TikoTikTok/bsidestlv-2026-badge/assets/characters/alice/alice_walk_sheet.png

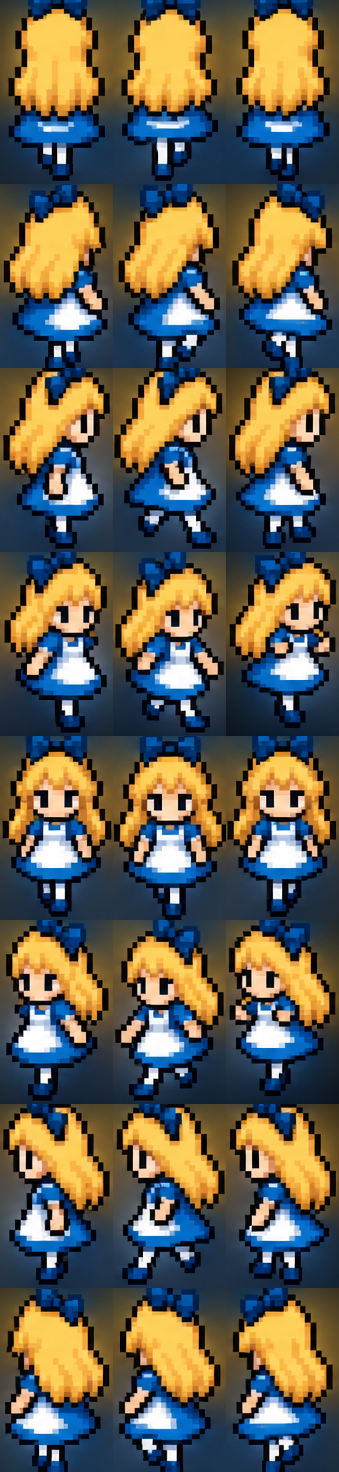
assets/characters/alice/alice_walk_sheet.png
