TikoTikTok/bsidestlv-2026-badge/software/dist/atlas.png

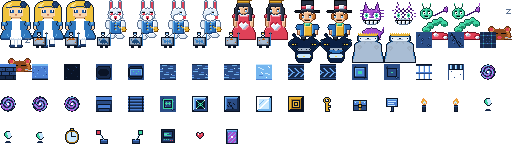
software/dist/atlas.png
