TikoTikTok/bsidestlv-2026-badge/software/dist/contact-sheet.png

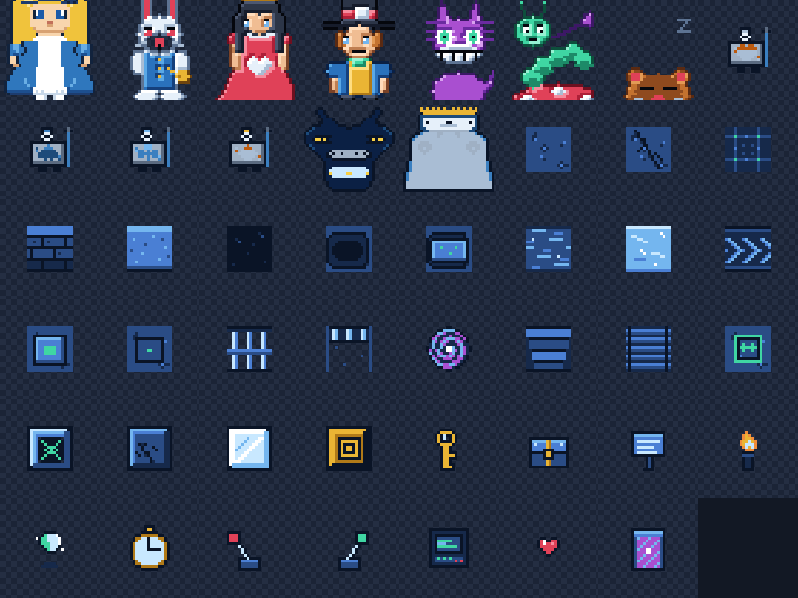
software/dist/contact-sheet.png
