TikoTikTok/bsidestlv-2026-badge/software/references/alice-reference.png

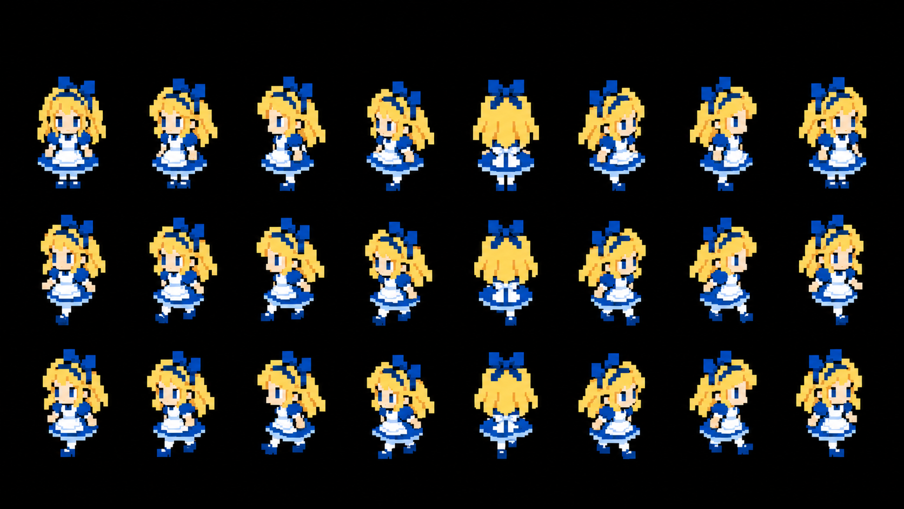
software/references/alice-reference.png
