TikoTikTok/bsidestlv-2026-badge/software/references/assets-reference2.png

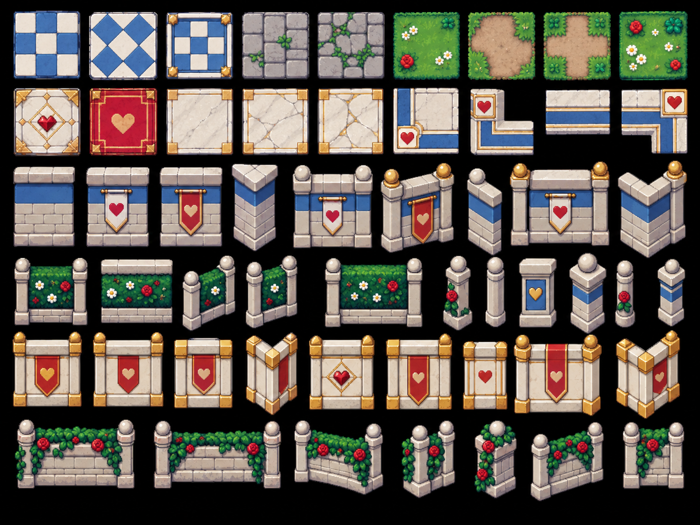
software/references/assets-reference2.png
