TikoTikTok/bsidestlv-2026-badge/software/references/assets-reference.png

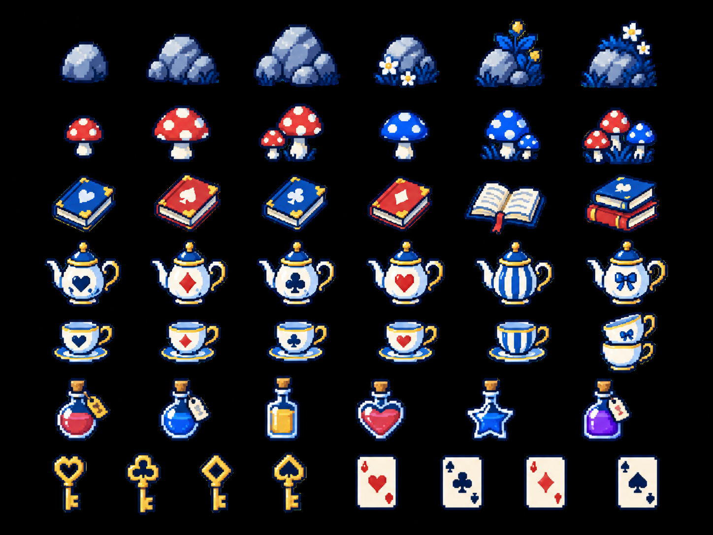
software/references/assets-reference.png
