TikoTikTok/bsidestlv-2026-badge/software/references/cheshire-reference.png

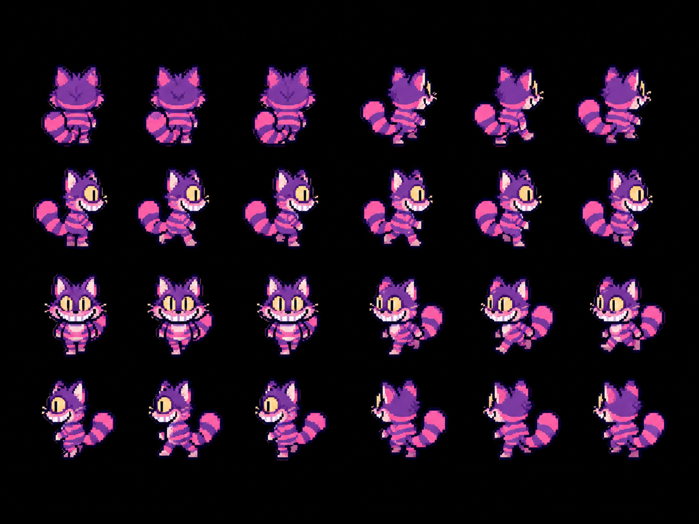
software/references/cheshire-reference.png
