TikoTikTok/bsidestlv-2026-badge/software/references/mad-hatter-reference.png

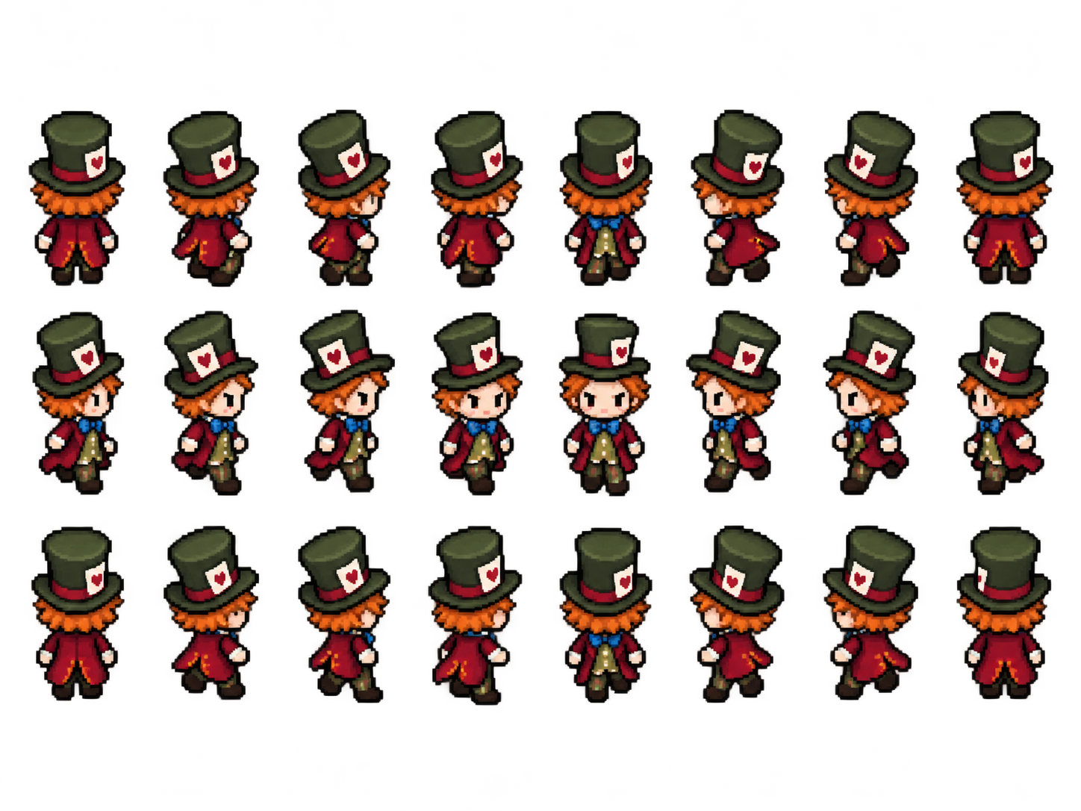
software/references/mad-hatter-reference.png
