TikoTikTok/bsidestlv-2026-badge/software/references/queen-reference.png

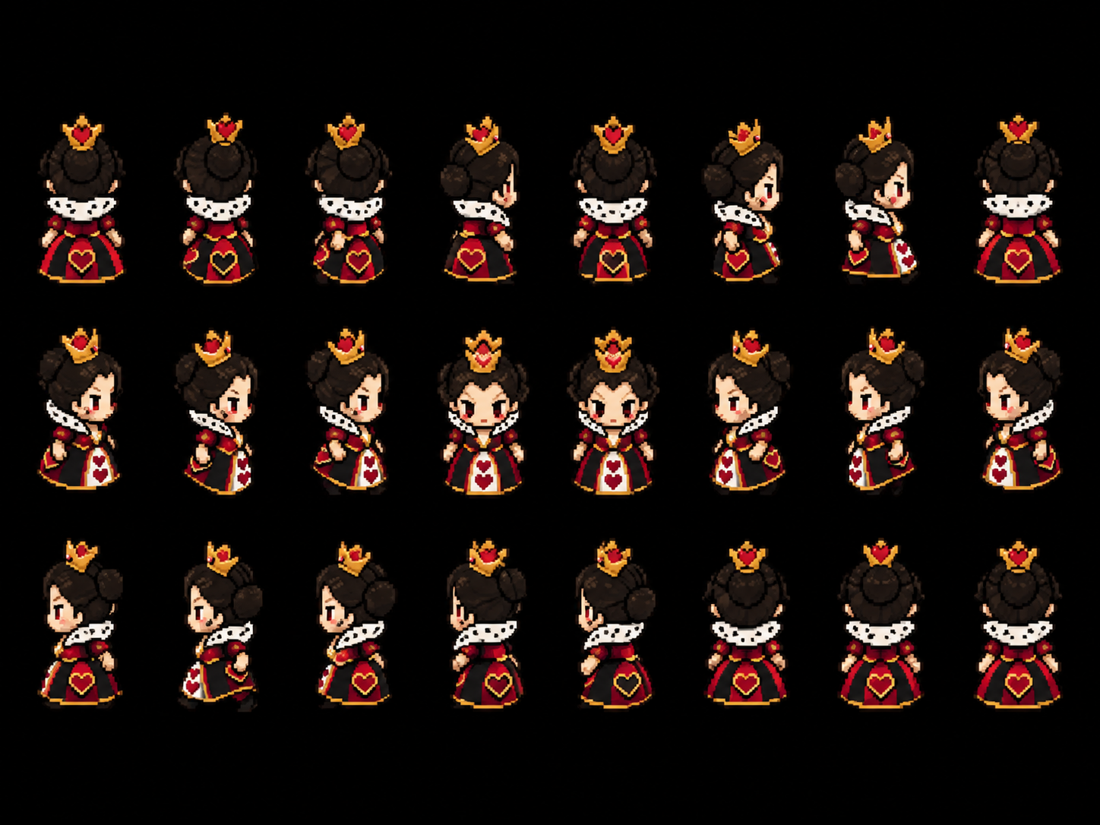
software/references/queen-reference.png
