TikoTikTok/bsidestlv-2026-badge/software/references/tiles-reference.png

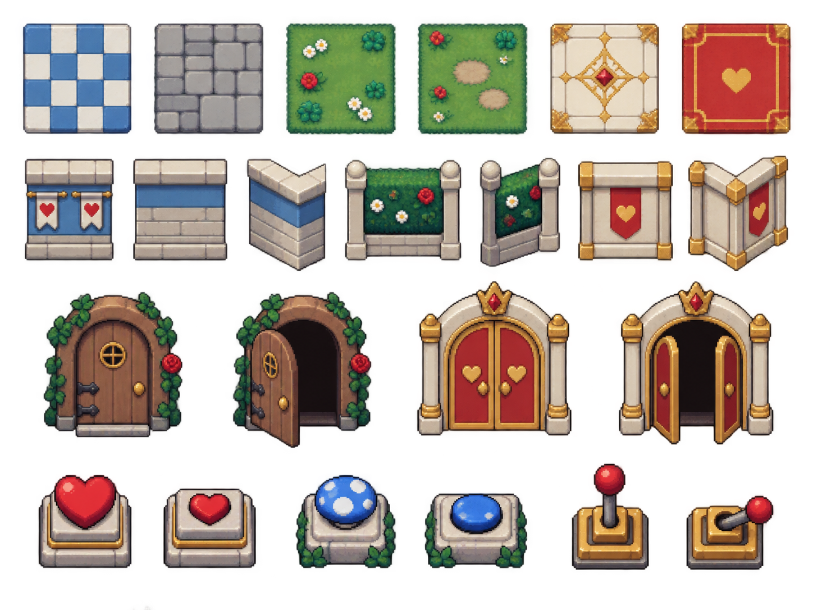
software/references/tiles-reference.png
