TikoTikTok/bsidestlv-2026-badge/software/references/white-rabbit-reference.png

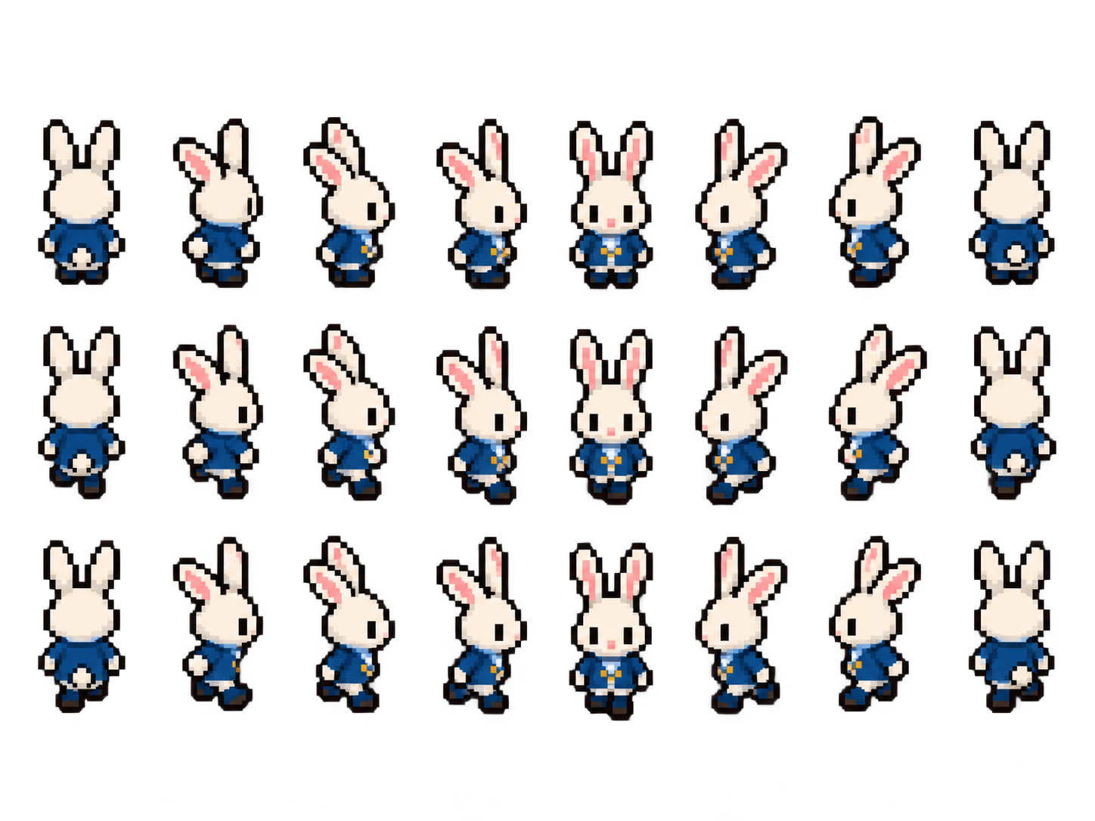
software/references/white-rabbit-reference.png
